buppu3/tnCart/KiCad/tnCart_rev2/tnCart_rev2.kicad_sch

## KiCad design KiCad/tnCart_rev2/tnCart_rev2.kicad_sch (2024-10-20)

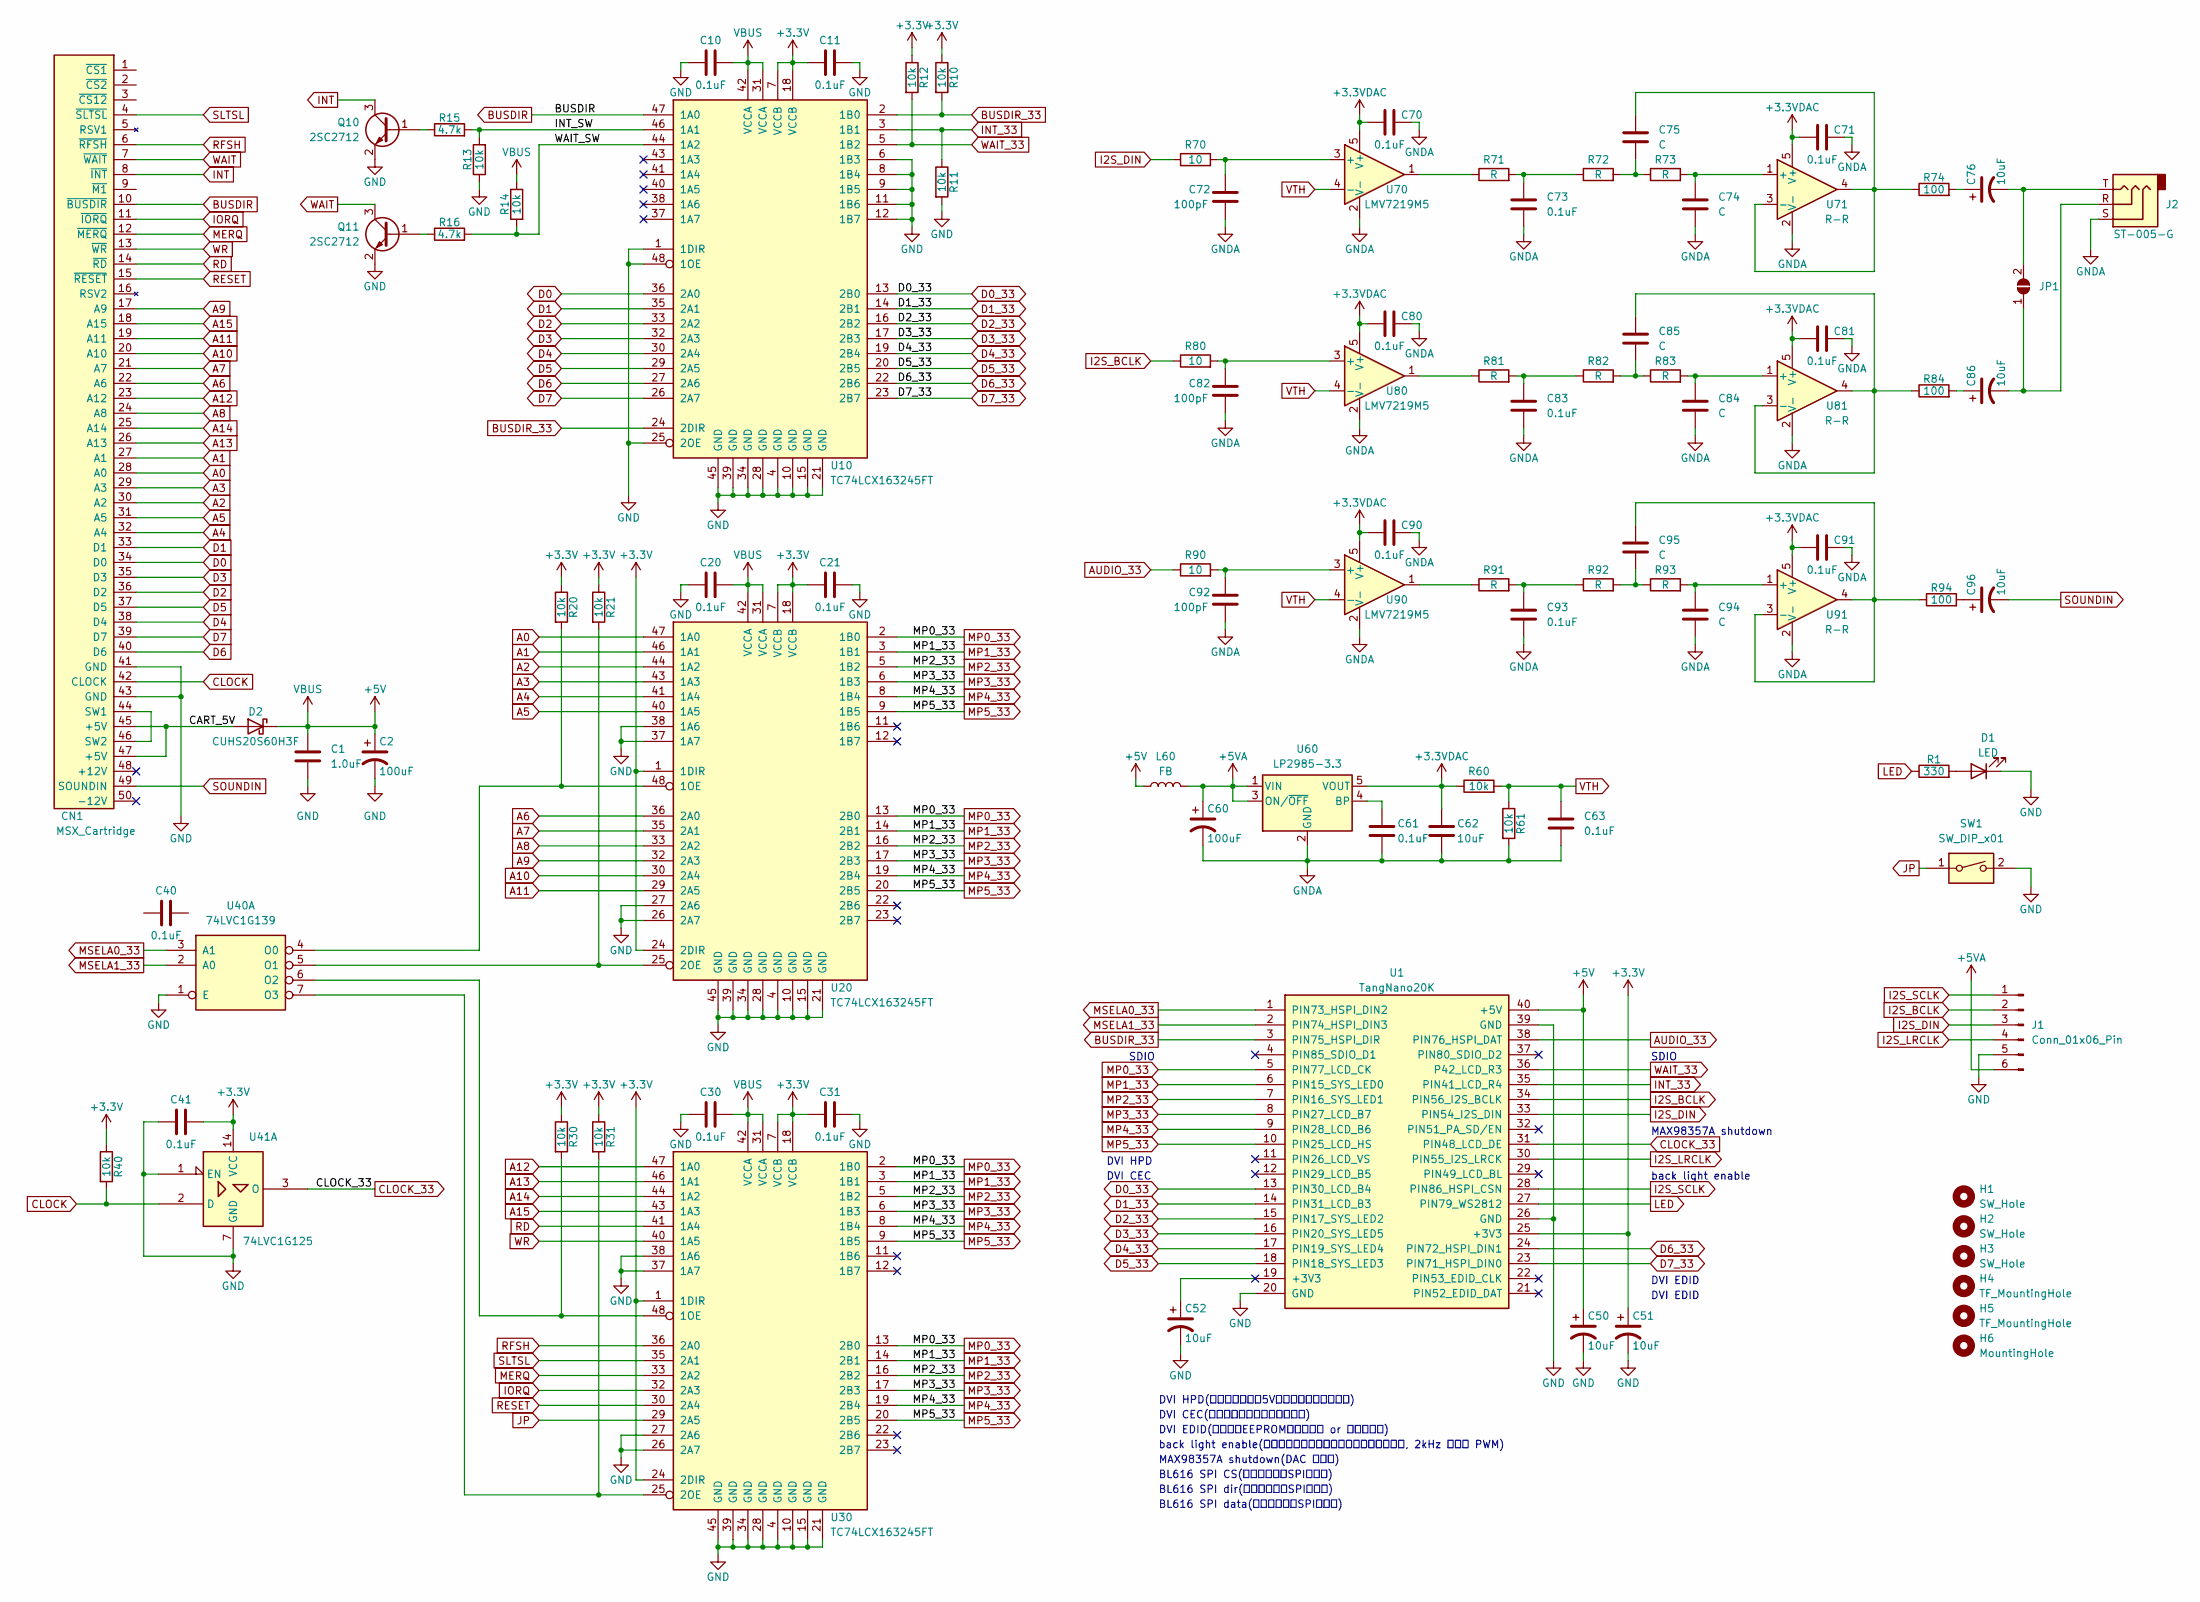
[picture p16: schematic tnCart_rev2.kicad_sch]

Parts:
C1: 1.0uF; C_0805_2012Metric_Pad1.18x1.45mm_HandSolder
C2, C60: 100uF; CP_Radial_D4.0mm_P1.50mm_Horz
C10, C11, C20, C21, C30, C31, C40, C41: 0.1uF; C_0805_2012Metric_Pad1.18x1.45mm_HandSolder
C50, C51, C52, C76, C86, C96: 10uF; CP_Radial_D4.0mm_P1.50mm_Horz
C61, C63, C70, C71, C73, C80, C81, C83, C90, C91, C93: 0.1uF
C62: 10uF
C72, C82, C92: 100pF
C74, C75, C84, C85, C94, C95: C
CN1: MSX_Cartridge; MSX_CardEdge
D1: LED; LED_D3.0mm
D2: CUHS20S60H3F; SOD-323HE_US2H
H1, H2, H3: SW_Hole; MountingHole_3.2mm_M3
H4, H5: TF_MountingHole; MountingHole_3.2mm_M3
H6: MountingHole; MountingHole_6mm
J1: Conn_01x06_Pin
J2: ST-005-G; Jack_3.5mm_Switronic_ST-005-G_horizontal
JP1: (no value)
L60: FB
Q10, Q11: 2SC2712; SC-59
R1: 330; R_0805_2012Metric_Pad1.20x1.40mm_HandSolder
R10, R11, R12, R13, R14, R20, R21, R30, R31, R40, R61: 10k; R_0805_2012Metric_Pad1.20x1.40mm_HandSolder
R15, R16: 4.7k; R_0805_2012Metric_Pad1.20x1.40mm_HandSolder
R60: 10k
R70, R80, R90: 10
R71, R72, R73, R81, R82, R83, R91, R92, R93: R
R74, R84, R94: 100; R_0805_2012Metric_Pad1.20x1.40mm_HandSolder
SW1: SW_DIP_x01
U1: TangNano20K; TangNano20k
U10, U20, U30: TC74LCX163245FT; TSSOP-48_6.1x12.5mm_P0.5mm
U40: 74LVC1G139
U41: 74LVC1G125
U60: LP2985-3.3; SOT-23-5
U70, U80, U90: LMV7219M5; SOT-23-5
U71, U81, U91: R-R; SOT-23-5

Connections:
+3.3V: C11.1, C21.1, C31.1, C41.2, C51.1, R10.1, R12.1, R20.1, R21.1, R30.1, R31.1, R40.1, U1.25 (+3V3), U10.7 (VCCB), U10.18 (VCCB), U20.1 (1DIR), U20.7 (VCCB), U20.18 (VCCB), U20.24 (2DIR), U30.1 (1DIR), U30.7 (VCCB), U30.18 (VCCB), U30.24 (2DIR), U41.14 (VCC)
+3.3VDAC: C62.1, C70.1, C71.1, C80.1, C81.1, C90.1, C91.1, R60.1, U60.5 (VOUT), U70.5 (V+), U71.5 (V+), U80.5 (V+), U81.5 (V+), U90.5 (V+), U91.5 (V+)
+5V: C1.1, C2.1, C10.2, C20.2, C30.2, C50.1, D2.1 (K), L60.1, R14.1, U1.40 (+5V), U10.31 (VCCA), U10.42 (VCCA), U20.31 (VCCA), U20.42 (VCCA), U30.31 (VCCA), U30.42 (VCCA)
+5VA: C60.1, J1.6, L60.2, U60.1 (VIN), U60.3 (ON/~OFF)
A0: CN1.28 (A0), U20.47 (1A0)
A1: CN1.27 (A1), U20.46 (1A1)
A2: CN1.30 (A2), U20.44 (1A2)
A3: CN1.29 (A3), U20.43 (1A3)
A4: CN1.32 (A4), U20.41 (1A4)
A5: CN1.31 (A5), U20.40 (1A5)
A6: CN1.22 (A6), U20.36 (2A0)
A7: CN1.21 (A7), U20.35 (2A1)
A8: CN1.24 (A8), U20.33 (2A2)
A9: CN1.17 (A9), U20.32 (2A3)
A10: CN1.20 (A10), U20.30 (2A4)
A11: CN1.19 (A11), U20.29 (2A5)
A12: CN1.23 (A12), U30.47 (1A0)
A13: CN1.26 (A13), U30.46 (1A1)
A14: CN1.25 (A14), U30.44 (1A2)
A15: CN1.18 (A15), U30.43 (1A3)
AUDIO_33: R90.1, U1.38 (PIN76_HSPI_DAT)
BUSDIR: CN1.10 (~BUSDIR), U10.47 (1A0)
BUSDIR_33: R10.2, U1.3 (PIN75_HSPI_DIR), U10.2 (1B0), U10.24 (2DIR)
CART_5V: CN1.45 (+5V), CN1.47 (+5V), D2.2 (A)
CLOCK: CN1.42 (CLOCK), R40.2, U41.2 (D)
CLOCK_33: U1.31 (PIN48_LCD_DE), U41.3 (O)
D0: CN1.34 (D0), U10.36 (2A0)
D0_33: U1.13 (PIN30_LCD_B4), U10.13 (2B0)
D1: CN1.33 (D1), U10.35 (2A1)
D1_33: U1.14 (PIN31_LCD_B3), U10.14 (2B1)
D2: CN1.36 (D2), U10.33 (2A2)
D2_33: U1.15 (PIN17_SYS_LED2), U10.16 (2B2)
D3: CN1.35 (D3), U10.32 (2A3)
D3_33: U1.16 (PIN20_SYS_LED5), U10.17 (2B3)
D4: CN1.38 (D4), U10.30 (2A4)
D4_33: U1.17 (PIN19_SYS_LED4), U10.19 (2B4)
D5: CN1.37 (D5), U10.29 (2A5)
D5_33: U1.18 (PIN18_SYS_LED3), U10.20 (2B5)
D6: CN1.40 (D6), U10.27 (2A6)
D6_33: U1.24 (PIN72_HSPI_DIN1), U10.22 (2B6)
D7: CN1.39 (D7), U10.26 (2A7)
D7_33: U1.23 (PIN71_HSPI_DIN0), U10.23 (2B7)
GND: C1.2, C2.2, C10.1, C11.2, C20.1, C21.2, C30.1, C31.2, C41.1, C50.2, C51.2, C52.2, CN1.41 (GND), CN1.43 (GND), D1.1 (K), J1.5, Q10.2 (E), Q11.2 (E), R11.2, R13.1, SW1.2, U1.20 (GND), U1.26 (GND), U1.39 (GND), U10.1 (1DIR), U10.4 (GND), U10.6 (1B3), U10.8 (1B4), U10.9 (1B5), U10.10 (GND), U10.11 (1B6), U10.12 (1B7), U10.15 (GND), U10.21 (GND), U10.25 (2OE), U10.28 (GND), U10.34 (GND), U10.39 (GND), U10.45 (GND), U10.48 (1OE), U20.4 (GND), U20.10 (GND), U20.15 (GND), U20.21 (GND), U20.26 (2A7), U20.27 (2A6), U20.28 (GND), U20.34 (GND), U20.37 (1A7), U20.38 (1A6), U20.39 (GND), U20.45 (GND), U30.4 (GND), U30.10 (GND), U30.15 (GND), U30.21 (GND), U30.26 (2A7), U30.27 (2A6), U30.28 (GND), U30.34 (GND), U30.37 (1A7), U30.38 (1A6), U30.39 (GND), U30.45 (GND), U40.1 (E), U41.1 (EN), U41.7 (GND)
GNDA: C60.2, C61.2, C62.2, C63.2, C70.2, C71.2, C72.2, C73.2, C74.2, C80.2, C81.2, C82.2, C83.2, C84.2, C90.2, C91.2, C92.2, C93.2, C94.2, J2.S, R61.2, U60.2 (GND), U70.2 (V-), U71.2 (V-), U80.2 (V-), U81.2 (V-), U90.2 (V-), U91.2 (V-)
I2S_BCLK: J1.2, R80.1, U1.34 (PIN56_I2S_BCLK)
I2S_DIN: J1.3, R70.1, U1.33 (PIN54_I2S_DIN)
I2S_LRCLK: J1.4, U1.30 (PIN55_I2S_LRCK)
I2S_SCLK: J1.1, U1.28 (PIN86_HSPI_CSN)
INT: CN1.8 (~INT), Q10.3 (C)
INT_33: R11.1, U1.35 (PIN41_LCD_R4), U10.3 (1B1)
INT_SW: R13.2, R15.2, U10.46 (1A1)
IORQ: CN1.11 (~IORQ), U30.32 (2A3)
JP: SW1.1, U30.29 (2A5)
LED: R1.1, U1.27 (PIN79_WS2812)
MERQ: CN1.12 (~MERQ), U30.33 (2A2)
MP0_33: U1.5 (PIN77_LCD_CK), U20.2 (1B0), U20.13 (2B0), U30.2 (1B0), U30.13 (2B0)
MP1_33: U1.6 (PIN15_SYS_LED0), U20.3 (1B1), U20.14 (2B1), U30.3 (1B1), U30.14 (2B1)
MP2_33: U1.7 (PIN16_SYS_LED1), U20.5 (1B2), U20.16 (2B2), U30.5 (1B2), U30.16 (2B2)
MP3_33: U1.8 (PIN27_LCD_B7), U20.6 (1B3), U20.17 (2B3), U30.6 (1B3), U30.17 (2B3)
MP4_33: U1.9 (PIN28_LCD_B6), U20.8 (1B4), U20.19 (2B4), U30.8 (1B4), U30.19 (2B4)
MP5_33: U1.10 (PIN25_LCD_HS), U20.9 (1B5), U20.20 (2B5), U30.9 (1B5), U30.20 (2B5)
MSELA0_33: U1.1 (PIN73_HSPI_DIN2), U40.3 (A1)
MSELA1_33: U1.2 (PIN74_HSPI_DIN3), U40.2 (A0)
unnamed: C52.1, U1.19 (+3V3)
unnamed: C61.1, U60.4 (BP)
unnamed: C72.1, R70.2, U70.3 (+)
unnamed: C73.1, R71.2, R72.1
unnamed: C74.1, R73.2, U71.1 (+)
unnamed: C75.1, R74.1, U71.3 (-), U71.4
unnamed: C75.2, R72.2, R73.1
unnamed: C76.1, R74.2
unnamed: C76.2, J2.T, JP1.2 (B)
unnamed: C82.1, R80.2, U80.3 (+)
unnamed: C83.1, R81.2, R82.1
unnamed: C84.1, R83.2, U81.1 (+)
unnamed: C85.1, R84.1, U81.3 (-), U81.4
unnamed: C85.2, R82.2, R83.1
unnamed: C86.1, R84.2
unnamed: C86.2, J2.R, JP1.1 (A)
unnamed: C92.1, R90.2, U90.3 (+)
unnamed: C93.1, R91.2, R92.1
unnamed: C94.1, R93.2, U91.1 (+)
unnamed: C95.1, R94.1, U91.3 (-), U91.4
unnamed: C95.2, R92.2, R93.1
unnamed: C96.1, R94.2
unnamed: CN1.44 (SW1), CN1.46 (SW2)
unnamed: D1.2 (A), R1.2
unnamed: Q10.1 (B), R15.1
unnamed: Q11.1 (B), R16.1
unnamed: R20.2, U20.48 (1OE), U40.4 (O0)
unnamed: R21.2, U20.25 (2OE), U40.5 (O1)
unnamed: R30.2, U30.48 (1OE), U40.6 (O2)
unnamed: R31.2, U30.25 (2OE), U40.7 (O3)
unnamed: R71.1, U70.1
unnamed: R81.1, U80.1
unnamed: R91.1, U90.1
RD: CN1.14 (~RD), U30.41 (1A4)
RESET: CN1.15 (~RESET), U30.30 (2A4)
RFSH: CN1.6 (~RFSH), U30.36 (2A0)
SLTSL: CN1.4 (~SLTSL), U30.35 (2A1)
SOUNDIN: C96.2, CN1.49 (SOUNDIN)
VTH: C63.1, R60.2, R61.1, U70.4 (-), U80.4 (-), U90.4 (-)
WAIT: CN1.7 (~WAIT), Q11.3 (C)
WAIT_33: R12.2, U1.36 (P42_LCD_R3), U10.5 (1B2)
WAIT_SW: R14.2, R16.2, U10.44 (1A2)
WR: CN1.13 (~WR), U30.40 (1A5)

Notes on the sheet:
SDIO
DVI HPD(モニタ接続時に5Vを分圧した電圧が入る)
BL616 SPI dir(マイコンとのSPI通信用)
DVI CEC(モニタと双方向の通信を行う)
back light enable(バックライト用のブーストコンバータ制御, 2kHz までの PWM)
DVI HPD
BL616 SPI CS(マイコンとのSPI通信用)
DVI CEC
MAX98357A shutdown
DVI EDID(モニタのEEPROMを読み出す or 双方向通信)
DVI EDID
BL616 SPI data(マイコンとのSPI通信用)
back light enable
MAX98357A shutdown(DAC の制御)
