buppu3/tnCart/rtl/src/peripheral/msx/pacrom_controller.sv

//
// pacrom_controller.sv
//
// BSD 3-Clause License
// 
// Copyright (c) 2024, Shinobu Hashimoto
// 
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
// 3. Neither the name of the copyright holder nor the names of its
//    contributors may be used to endorse or promote products derived from
//    this software without specific prior written permission.
// 
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

`default_nettype none

/***************************************************************
 * PAC ROM コントローラ
 ***************************************************************/
module PACROM_CONTROLLER #(
    parameter               RAM_ADDR_BIOS = 0,
    parameter               RAM_ADDR_PAC = 0,
    parameter               COUNT = 1,
    parameter               USE_FF = 0
) (
    input   wire            RESET_n,
    input   wire            CLK,
    BUS_IF.CARTRIDGE        Bus,
    RAM_IF.HOST             Ram,
    BUS_IF.MSX              ExtBus[0:COUNT-1],
    output wire             SramEnable
);
    localparam [15:0] BankAddr = 16'h5FFE;
    localparam [15:0] BankKey = 16'h694D;

    /***************************************************************
     * external signal
     ***************************************************************/
    logic [7:0] tmp_dout[0:COUNT-1];
    logic tmp_busdir_n[0:COUNT-1];
    logic tmp_int_n[0:COUNT-1];
    logic tmp_wait_n[0:COUNT-1];
    generate
        genvar num;
        for(num = 0; num < COUNT; num = num + 1) begin: extbus_loop
            if(USE_FF) begin
                always @(posedge CLK or negedge RESET_n) begin
                    if(!RESET_n) begin
                        ExtBus[num].ADDR        <= 0;
                        ExtBus[num].DIN         <= 0;
                        ExtBus[num].RFSH_n      <= 1;
                        ExtBus[num].RD_n        <= 1;
                        ExtBus[num].WR_n        <= 1;
                        ExtBus[num].MERQ_n      <= 1;
                        ExtBus[num].IORQ_n      <= 1;
                        ExtBus[num].CS1_n       <= 1;
                        ExtBus[num].CS2_n       <= 1;
                        ExtBus[num].CS12_n      <= 1;
                        ExtBus[num].M1_n        <= 1;
                        ExtBus[num].SLTSL_n     <= 1;
                        ExtBus[num].RESET_n     <= 0;
                        ExtBus[num].CLK         <= 0;
                        ExtBus[num].CLK_EN      <= 0;
                    end
                    else if(!Bus.RESET_n) begin
                        ExtBus[num].ADDR        <= 0;
                        ExtBus[num].DIN         <= 0;
                        ExtBus[num].RFSH_n      <= Bus.RFSH_n;
                        ExtBus[num].RD_n        <= 1;
                        ExtBus[num].WR_n        <= 1;
                        ExtBus[num].MERQ_n      <= 1;
                        ExtBus[num].IORQ_n      <= 1;
                        ExtBus[num].CS1_n       <= 1;
                        ExtBus[num].CS2_n       <= 1;
                        ExtBus[num].CS12_n      <= 1;
                        ExtBus[num].M1_n        <= 1;
                        ExtBus[num].SLTSL_n     <= 1;
                        ExtBus[num].RESET_n     <= 0;
                        ExtBus[num].CLK         <= Bus.CLK;
                        ExtBus[num].CLK_EN      <= Bus.CLK_EN;
                    end
                    else begin
                        ExtBus[num].ADDR        <= Bus.ADDR;
                        ExtBus[num].DIN         <= Bus.DIN;
                        ExtBus[num].RFSH_n      <= Bus.RFSH_n;
                        ExtBus[num].RD_n        <= Bus.RD_n;
                        ExtBus[num].WR_n        <= Bus.WR_n;
                        ExtBus[num].MERQ_n      <= Bus.MERQ_n;
                        ExtBus[num].IORQ_n      <= Bus.IORQ_n;
                        ExtBus[num].CS1_n       <= Bus.CS1_n;
                        ExtBus[num].CS2_n       <= Bus.CS2_n;
                        ExtBus[num].CS12_n      <= Bus.CS12_n;
                        ExtBus[num].M1_n        <= Bus.M1_n;
                        ExtBus[num].SLTSL_n     <= Bus.SLTSL_n;
                        ExtBus[num].RESET_n     <= Bus.RESET_n;
                        ExtBus[num].CLK         <= Bus.CLK;
                        ExtBus[num].CLK_EN      <= Bus.CLK_EN;
                    end
                end
            end
            else begin
                assign ExtBus[num].ADDR        = Bus.ADDR;
                assign ExtBus[num].DIN         = Bus.DIN;
                assign ExtBus[num].RFSH_n      = Bus.RFSH_n;
                assign ExtBus[num].RD_n        = Bus.RD_n;
                assign ExtBus[num].WR_n        = Bus.WR_n;
                assign ExtBus[num].MERQ_n      = Bus.MERQ_n;
                assign ExtBus[num].IORQ_n      = Bus.IORQ_n;
                assign ExtBus[num].CS1_n       = Bus.CS1_n;
                assign ExtBus[num].CS2_n       = Bus.CS2_n;
                assign ExtBus[num].CS12_n      = Bus.CS12_n;
                assign ExtBus[num].M1_n        = Bus.M1_n;
                assign ExtBus[num].SLTSL_n     = Bus.SLTSL_n;
                assign ExtBus[num].RESET_n     = Bus.RESET_n;
                assign ExtBus[num].CLK         = Bus.CLK;
                assign ExtBus[num].CLK_EN      = Bus.CLK_EN;
            end

            assign ExtBus[num].CLK_21M = Bus.CLK_21M;
            assign ExtBus[num].CLK_EN_21M = Bus.CLK_EN_21M;

            assign tmp_dout    [num] = ExtBus[num].DOUT     | ((num < COUNT-1) ? tmp_dout    [num + 1] : 0);
            assign tmp_busdir_n[num] = ExtBus[num].BUSDIR_n & ((num < COUNT-1) ? tmp_busdir_n[num + 1] : 1);
            assign tmp_int_n   [num] = ExtBus[num].INT_n    & ((num < COUNT-1) ? tmp_int_n   [num + 1] : 1);
            assign tmp_wait_n  [num] = ExtBus[num].WAIT_n   & ((num < COUNT-1) ? tmp_wait_n  [num + 1] : 1);
        end
    endgenerate

    if(USE_FF) begin
        always @(posedge CLK or negedge RESET_n) begin
            if(!RESET_n) begin
                Bus.INT_n          <= 1;
                Bus.WAIT_n         <= 1;
            end
            else if(!Bus.RESET_n) begin
                Bus.INT_n          <= 1;
                Bus.WAIT_n         <= 1;
            end
            else begin
                Bus.INT_n          <= tmp_int_n[0];
                Bus.WAIT_n         <= tmp_wait_n[0];
            end
        end
    end
    else begin
        assign Bus.INT_n          = tmp_int_n[0];
        assign Bus.WAIT_n         = tmp_wait_n[0];
    end

    /***************************************************************
     * アドレスデコード
     ***************************************************************/
    wire cs1_n  =  Bus.ADDR[15] || ~Bus.ADDR[14];

    /***************************************************************
     * memory read / write strobe
     ***************************************************************/
    wire wr_n = Bus.SLTSL_n || Bus.MERQ_n || Bus.WR_n;
    wire rd_n = Bus.SLTSL_n || Bus.MERQ_n || Bus.RD_n;
    wire wr_mem_n  = cs1_n || wr_n || !bank_pac;
    wire rd_mem_n  = cs1_n || rd_n;

    /***************************************************************
     * ライト検出
     ***************************************************************/
    logic prev_wr_n;
    always_ff @(posedge CLK or negedge RESET_n) begin
        if(!RESET_n)          prev_wr_n <= 1;
        else if(!Bus.RESET_n) prev_wr_n <= 1;
        else                  prev_wr_n <= wr_n;
    end
    wire det_wr = prev_wr_n && !wr_n;

    /***************************************************************
     * bank register
     ***************************************************************/
    reg [7:0] BankReg[0:1];

    always_ff @(posedge CLK or negedge RESET_n) begin
        if(!RESET_n) begin
            BankReg[0] <= 0;
            BankReg[1] <= 0;
        end
        else if(!Bus.RESET_n) begin
            BankReg[0] <= 0;
            BankReg[1] <= 0;
        end
        else if(det_wr && (Bus.ADDR[15:1] == BankAddr[15:1])) begin
            BankReg[Bus.ADDR[0]] <= Bus.DIN;
        end
    end

    /***************************************************************
     * address
     ***************************************************************/
    assign SramEnable = (BankReg[0] == BankKey[7:0]) && (BankReg[1] == BankKey[15:8]);
    wire bank_pac = SramEnable && (Bus.ADDR[15:13] == 2'b010);
    wire [23:0] addr = bank_pac ? {RAM_ADDR_PAC[23:13], Bus.ADDR[12:0]} : {RAM_ADDR_BIOS[23:14], Bus.ADDR[13:0]};

    /***************************************************************
     * memory r/w
     ***************************************************************/
    if(USE_FF) begin
        always_ff @(posedge CLK or negedge RESET_n) begin
            if(!RESET_n) begin
                Ram.ADDR <= 0;
                Ram.WE_n <= 1;
                Ram.DIN <= 0;
                Ram.DIN_SIZE <= RAM::DIN_SIZE_8;
                Ram.OE_n <= 1;
                Bus.BUSDIR_n <= 1;
                Bus.DOUT <= 0;
                Ram.RFSH_n <= 1;
            end
            else if(!Bus.RESET_n) begin
                Ram.ADDR <= 0;
                Ram.WE_n <= 1;
                Ram.DIN <= 0;
                Ram.DIN_SIZE <= RAM::DIN_SIZE_8;
                Ram.OE_n <= 1;
                Bus.BUSDIR_n <= 1;
                Bus.DOUT <= 0;
                Ram.RFSH_n <= Bus.RFSH_n;
            end
            else begin
                // address
                Ram.ADDR <= (rd_mem_n && wr_mem_n) ? 0 : addr[$bits(Ram.ADDR)-1:0];

                // memory write
                Ram.WE_n <= wr_mem_n;
                Ram.DIN <= wr_mem_n ? 0 : Bus.DIN;
                Ram.DIN_SIZE <= RAM::DIN_SIZE_8;

                // memory read
                Ram.OE_n <= rd_mem_n;
                Bus.BUSDIR_n <= rd_mem_n && tmp_busdir_n[0];
                Bus.DOUT <= tmp_busdir_n[0] ? (rd_mem_n ? 0 : Ram.DOUT[7:0]) : tmp_dout[0];

                // memory refresh
                Ram.RFSH_n <= Bus.RFSH_n;
            end
        end
    end
    else begin
        // address
        assign Ram.ADDR = (rd_mem_n && wr_mem_n) ? 0 : addr[$bits(Ram.ADDR)-1:0];

        // memory write
        assign Ram.DIN_SIZE = RAM::DIN_SIZE_8;
        assign Ram.DIN  = wr_mem_n ? 0 : Bus.DIN;
        assign Ram.WE_n = wr_mem_n;

        // memory read
        assign Ram.OE_n = rd_mem_n;
        assign Bus.BUSDIR_n = rd_mem_n && tmp_busdir_n[0];
        assign Bus.DOUT = tmp_busdir_n[0] ? (rd_mem_n ? 0 : Ram.DOUT[7:0]) : tmp_dout[0];

        // memory refresh
        assign Ram.RFSH_n = Bus.RFSH_n;
    end

endmodule


`default_nettype wire
