buppu3/tnCart/rtl/src/peripheral/sound/scc/scc.sv

//
// scc.sv
//
// BSD 3-Clause License
// 
// Copyright (c) 2024, Shinobu Hashimoto
// 
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
// 3. Neither the name of the copyright holder nor the names of its
//    contributors may be used to endorse or promote products derived from
//    this software without specific prior written permission.
// 
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

`default_nettype none

`define SCC_USE_DPB

/***************************************************************
 * SCC sound
 ***************************************************************/
module SCC (
    input wire          RESET_n,
    input wire          CLK,
    input wire          CLK_EN,

    input wire          MODE_SCC_I,

    input wire          CS_n,
    input wire [7:0]    ADDR,
    input wire          WR_n,
    input wire          RD_n,
    output wire         BUSDIR_n,
    input wire [7:0]    DIN,
    output wire [7:0]   DOUT,

    output reg [10:0]   OUT
);
    /***************************************************************
     * 読み書きタイミング
     ***************************************************************/
    wire rd_n = CS_n || RD_n;
    wire wr_n = CS_n || WR_n;
    logic prev_wr_n;
    always_ff @(posedge CLK or negedge RESET_n) begin
        if(!RESET_n)                 prev_wr_n <= 1;
        else if(!wr_n && !cs_test_n) prev_wr_n <= wr_n;
    end
    wire det_wr = prev_wr_n && !wr_n;
    wire det_rd = !rd_n;

    /***************************************************************
     * アドレスデコーダ
     ***************************************************************/
    wire cs_test_n = ADDR[7:5] != (MODE_SCC_I ? 3'b110 : 3'b111);
    wire cs_enable_n = ADDR != (MODE_SCC_I ? 8'hAF : 8'h8F);

    /***************************************************************
     * TEST レジスタ
     ***************************************************************/
    logic [7:0] test_reg;
    always_ff @(posedge CLK or negedge RESET_n) begin
        if(!RESET_n)                  test_reg <= 0;
        else if(det_wr && !cs_test_n) test_reg <= DIN;
    end

    /***************************************************************
     * ENABLE レジスタ
     ***************************************************************/
    logic [7:0] enable_reg;
    always_ff @(posedge CLK or negedge RESET_n) begin
        if(!RESET_n)                    enable_reg <= 0;
        else if(det_wr && !cs_enable_n) enable_reg <= DIN;
    end

    /***************************************************************
     * 出力更新カウンタ
     ***************************************************************/
    logic [3:0] out_cnt;
    always_ff @(posedge CLK or negedge RESET_n) begin
        if(!RESET_n)    out_cnt <= 0;
        else if(CLK_EN) out_cnt <= out_cnt + 1'd1;
    end
    wire OUT_EN = out_cnt == 0;

    /***************************************************************
     * 各チャンネルの処理
     ***************************************************************/
    logic busdir_n[0:4];
    logic [7:0] dout[0:4];
    logic [7:0] ch_out[0:4];

    generate
        genvar chnum;
        for(chnum = 0; chnum < 5; chnum = chnum + 1) begin: ch
            wire wr_freq_l = (ADDR[7:4] == (MODE_SCC_I ? 4'b1010 : 4'b1000)) && (ADDR[3:0] == chnum * 2 +  0);
            wire wr_freq_h = (ADDR[7:4] == (MODE_SCC_I ? 4'b1010 : 4'b1000)) && (ADDR[3:0] == chnum * 2 +  1);
            wire wr_vol    = (ADDR[7:4] == (MODE_SCC_I ? 4'b1010 : 4'b1000)) && (ADDR[3:0] == chnum     + 10);
            wire wr_wave   = (ADDR[7:5] == (MODE_SCC_I ? chnum[2:0] : (chnum[2] ? 3'd3 : chnum[2:0])));
            wire rd_wave   = (ADDR[7:5] == (MODE_SCC_I ? chnum[2:0] : (chnum[2] ? 3'd5 : chnum[2:0])));

            SCC_SIGNAL_GENERATOR u_gen (
                .RESET_n,
                .CLK,
                .CLK_EN,
                .TEST_CNTM  (test_reg[0]),
                .TEST_CNTH  (test_reg[1]),
                .TEST_ADDR  (test_reg[5]),
                .TEST_MEM   (chnum == 4 ? test_reg[7] : test_reg[6]),
                .ADDR       (ADDR[4:0]),
                .WR_FREQ_L_n(!det_wr || !wr_freq_l),
                .WR_FREQ_H_n(!det_wr || !wr_freq_h),
                .WR_VOL_n   (!det_wr || !wr_vol),
                .WR_WAVE_n  (!det_wr || !wr_wave),
                .RD_WAVE_n  (!det_rd || !rd_wave),
                .BUSDIR_n   (busdir_n[chnum]),
                .DIN,
                .DOUT       (dout[chnum]),
                .MUTE_n     (enable_reg[chnum]),
                .OUT_EN,
                .OUT        (ch_out[chnum])
            );
        end
    endgenerate

    /***************************************************************
     * 波形メモリのデータを CPU 側へ出力
     ***************************************************************/
    assign BUSDIR_n = busdir_n[0] && busdir_n[1] && busdir_n[2] && busdir_n[3] && busdir_n[4];
    assign DOUT = dout[0] | dout[1] | dout[2] | dout[3] | dout[4];

    /***************************************************************
     * ミキサー
     ***************************************************************/
    SCC_MIXER u_mixer (
        .RESET_n,
        .CLK,
        .CLK_EN(CLK_EN && OUT_EN),
        .IN(ch_out),
        .OUT(OUT)
    );
endmodule

/***********************************************************************
 * ミキサー
 ***********************************************************************/
module SCC_MIXER (
    input wire          RESET_n,
    input wire          CLK,
    input wire          CLK_EN,
    input wire [7:0]    IN[0:4],
    output reg [10:0]   OUT
);

    logic [10:0] in_0;
    always_ff @(posedge CLK or negedge RESET_n) begin
        if(!RESET_n)    in_0 <= 0;
        else if(CLK_EN) in_0 <= IN[0][7] ? {3'b111,IN[0]} : {3'b000,IN[0]};
    end

    logic [10:0] in_1;
    always_ff @(posedge CLK or negedge RESET_n) begin
        if(!RESET_n)    in_1 <= 0;
        else if(CLK_EN) in_1 <= IN[1][7] ? {3'b111,IN[1]} : {3'b000,IN[1]};
    end

    logic [10:0] in_2;
    always_ff @(posedge CLK or negedge RESET_n) begin
        if(!RESET_n)    in_2 <= 0;
        else if(CLK_EN) in_2 <= IN[2][7] ? {3'b111,IN[2]} : {3'b000,IN[2]};
    end

    logic [10:0] in_3;
    always_ff @(posedge CLK or negedge RESET_n) begin
        if(!RESET_n)    in_3 <= 0;
        else if(CLK_EN) in_3 <= IN[3][7] ? {3'b111,IN[3]} : {3'b000,IN[3]};
    end

    logic [10:0] in_4;
    always_ff @(posedge CLK or negedge RESET_n) begin
        if(!RESET_n)    in_4 <= 0;
        else if(CLK_EN) in_4 <= IN[4][7] ? {3'b111,IN[4]} : {3'b000,IN[4]};
    end

    always_ff @(posedge CLK or negedge RESET_n) begin
        if(!RESET_n)    OUT <= 0;
        else if(CLK_EN) OUT <= in_0 + in_1 + in_2 + in_3 + in_4;
    end

endmodule

/***********************************************************************
 * SCC 1CH シグナルジェネレータ
 ***********************************************************************/
module SCC_SIGNAL_GENERATOR (
    input wire          RESET_n,
    input wire          CLK,
    input wire          CLK_EN,

    input wire          TEST_CNTM,      // TEST.b0
    input wire          TEST_CNTH,      // TEST.b1
    input wire          TEST_ADDR,      // TEST.b5
    input wire          TEST_MEM,       // TEST.b6(ch0~3), TEST.b7(ch4)

    input wire [4:0]    ADDR,
    input wire          WR_FREQ_L_n,
    input wire          WR_FREQ_H_n,
    input wire          WR_VOL_n,
    input wire          WR_WAVE_n,
    input wire          RD_WAVE_n,
    output wire         BUSDIR_n,
    input wire  [7:0]   DIN,
    output wire  [7:0]  DOUT,

    input wire          MUTE_n,
    input wire          OUT_EN,
    output reg [7:0]    OUT
);

    logic [4:0] WAVE_ADDR;
    SCC_COUNTER u_cnt (
        .RESET_n,
        .CLK,
        .CLK_EN,
        .TEST_CNTM,
        .TEST_CNTH,
        .TEST_ADDR,
        .WR_FREQ_L_n,
        .WR_FREQ_H_n,
        .DIN,
        .WAVE_ADDR
    );

    wire [7:0] WAVE_DATA;
    SCC_WAVE_MEMORY u_mem (
        .RESET_n,
        .CLK,
        .TEST_MEM,
        .ADDR(ADDR[4:0]),
        .RD_WAVE_n,
        .WR_WAVE_n,
        .DIN,
        .BUSDIR_n,
        .DOUT,
        .WAVE_ADDR,
        .WAVE_DATA
    );

    SCC_AMP u_amp (
        .RESET_n,
        .CLK,
        .CLK_EN,
        .WR_VOL_n,
        .DIN(DIN[3:0]),
        .WAVE_DATA,
        .MUTE_n,
        .OUT_EN,
        .OUT
    );
endmodule

/***********************************************************************
 * SCC CH カウンター
 ***********************************************************************/
module SCC_COUNTER (
    input wire          RESET_n,
    input wire          CLK,
    input wire          CLK_EN,

    input wire          TEST_CNTM,      // TEST.b0
    input wire          TEST_CNTH,      // TEST.b1
    input wire          TEST_ADDR,      // TEST.b5

    input wire          WR_FREQ_L_n,
    input wire          WR_FREQ_H_n,
    input wire [7:0]    DIN,

    output reg [4:0]    WAVE_ADDR
);

    /***************************************************************
     * 分周レジスタライト
     ***************************************************************/
    logic [3:0] freq_l;
    logic [3:0] freq_m;
    logic [3:0] freq_h;
    always_ff @(posedge CLK or negedge RESET_n) begin
        if(!RESET_n) begin
            freq_l <= 0;
            freq_m <= 0;
            freq_h <= 0;
        end
        else if(!WR_FREQ_L_n) begin
            freq_l <= DIN[3:0];
            freq_m <= DIN[7:4];
        end
        else if(!WR_FREQ_H_n) begin
            freq_h <= DIN[3:0];
        end
    end

    /***************************************************************
     * カウンタの動作条件
     ***************************************************************/
    wire dec_cnt_l = CLK_EN;
    wire dec_cnt_m = (dec_cnt_l && (cnt_l == 0)) || TEST_CNTM;
    wire dec_cnt_h = (dec_cnt_m && (cnt_m == 0)) || TEST_CNTH;
    wire inc_adr   = (dec_cnt_h && (cnt_h == 0));
    wire rst_cnt   = inc_adr;
    wire rst_adr   = (TEST_ADDR && (!WR_FREQ_L_n || !WR_FREQ_H_n));

    /***************************************************************
     * 分周カウント
     ***************************************************************/
    logic [3:0] cnt_l;
    logic [3:0] cnt_m;
    logic [3:0] cnt_h;

    always_ff @(posedge CLK or negedge RESET_n) begin
        if(!RESET_n)       cnt_l <= 0;
        else if(rst_cnt)   cnt_l <= freq_l;
        else if(dec_cnt_l) cnt_l <= cnt_l - 1'd1;
    end

    always_ff @(posedge CLK or negedge RESET_n) begin
        if(!RESET_n)       cnt_m <= 0;
        else if(rst_cnt)   cnt_m <= freq_m;
        else if(dec_cnt_m) cnt_m <= cnt_m - 1'd1;
    end

    always_ff @(posedge CLK or negedge RESET_n) begin
        if(!RESET_n)       cnt_h <= 0;
        else if(rst_cnt)   cnt_h <= freq_h;
        else if(dec_cnt_h) cnt_h <= cnt_h - 1'd1;
    end

    /***************************************************************
     * アドレスカウント
     ***************************************************************/
    always_ff @(posedge CLK or negedge RESET_n) begin
        if(!RESET_n)       WAVE_ADDR <= 0;
        else if(rst_adr)   WAVE_ADDR <= 0;
        else if(inc_adr)   WAVE_ADDR <= WAVE_ADDR + 1'd1;
    end

endmodule

`ifdef SCC_USE_DPB
/***********************************************************************
 * SCC CH 波形メモリー(DPB)
 ***********************************************************************/
module SCC_WAVE_MEMORY (
    input wire          RESET_n,
    input wire          CLK,

    input wire          TEST_MEM,   // TEST.b6(ch0~3), TEST.b7(ch4)

    input wire [4:0]    ADDR,
    input wire          RD_WAVE_n,
    input wire          WR_WAVE_n,
    input wire  [7:0]   DIN,
    output wire         BUSDIR_n,
    output wire [7:0]   DOUT,

    input wire [4:0]    WAVE_ADDR,
    output wire  [7:0]  WAVE_DATA
);

    wire [7:0] dpb_read_a;  // DAC 側
    wire [7:0] dpb_read_b;  // CPU 側

    /***************************************************************
     * 波形出力
     ***************************************************************/
    assign WAVE_DATA = dpb_read_a;

    /***************************************************************
     * メモリリード
     ***************************************************************/
    assign DOUT = RD_WAVE_n ? 0 : (TEST_MEM ? dpb_read_a : dpb_read_b); // TEST_MEM == 1 の時は波形出力データを返す
    assign BUSDIR_n = RD_WAVE_n;

    /***************************************************************
     * メモリ
     ***************************************************************/
    wire [7:0] dpb_douta_w;
    wire [7:0] dpb_doutb_w;

    DPB u_dpb (
        .DOA({dpb_douta_w[7:0],dpb_read_a[7:0]}),
        .DOB({dpb_doutb_w[7:0],dpb_read_b[7:0]}),
        .CLKA(CLK),
        .OCEA(1'b1),
        .CEA(1'b1),
        .RESETA(!RESET_n),
        .WREA(1'b0),
        .CLKB(CLK),
        .OCEB(1'b1),
        .CEB(1'b1),
        .RESETB(!RESET_n),
        .WREB(!(WR_WAVE_n | TEST_MEM)),         // TEST_MEM == 1 の時はライト禁止
        .BLKSELA(3'b000),
        .BLKSELB(3'b000),
        .ADA({6'b000000,WAVE_ADDR[4:0],3'b000}),
        .DIA({8'b00000000,8'b00000000}),
        .ADB({6'b000000,ADDR[4:0],3'b000}),
        .DIB({8'b00000000,DIN[7:0]})
    );

    defparam u_dpb.READ_MODE0 = 1'b0;
    defparam u_dpb.READ_MODE1 = 1'b0;
    defparam u_dpb.WRITE_MODE0 = 2'b00;
    defparam u_dpb.WRITE_MODE1 = 2'b00;
    defparam u_dpb.BIT_WIDTH_0 = 8;
    defparam u_dpb.BIT_WIDTH_1 = 8;
    defparam u_dpb.BLK_SEL_0 = 3'b000;
    defparam u_dpb.BLK_SEL_1 = 3'b000;
    defparam u_dpb.RESET_MODE = "SYNC";
endmodule

`else

/***********************************************************************
 * SCC CH 波形メモリー(register)
 ***********************************************************************/
module SCC_WAVE_MEMORY (
    input wire          RESET_n,
    input wire          CLK,

    input wire          TEST_MEM,   // TEST.b6(ch0~3), TEST.b7(ch4)

    input wire [4:0]    ADDR,
    input wire          RD_WAVE_n,
    input wire          WR_WAVE_n,
    input wire  [7:0]   DIN,
    output reg          BUSDIR_n,
    output reg [7:0]    DOUT,

    input wire [4:0]    WAVE_ADDR,
    output reg  [7:0]   WAVE_DATA
);

    reg [7:0] buffer[0:31];

    /***************************************************************
     * メモリ R/W
     ***************************************************************/
    always_ff @(posedge CLK or negedge RESET_n) begin
        if(!RESET_n) begin
            BUSDIR_n <= 1;
            DOUT <= 0;
            WAVE_DATA <= 0;
        end
        else if(TEST_MEM) begin
            BUSDIR_n <= 1;
            DOUT <= 0;
            WAVE_DATA <= buffer[WAVE_ADDR];
        end
        else if(!WR_WAVE_n) begin
            BUSDIR_n <= 1;
            DOUT <= 0;
            WAVE_DATA <= DIN;
            buffer[ADDR] <= DIN;
        end
        else if(!RD_WAVE_n) begin
            BUSDIR_n <= 0;
            DOUT <= buffer[ADDR];
            WAVE_DATA <= buffer[ADDR];
        end
        else begin
            BUSDIR_n <= 1;
            DOUT <= 0;
            WAVE_DATA <= buffer[WAVE_ADDR];
        end
    end
endmodule

`endif

/***********************************************************************
 * SCC CH アンプ
 ***********************************************************************/
module SCC_AMP (
    input wire          RESET_n,
    input wire          CLK,
    input wire          CLK_EN,

    input wire          WR_VOL_n,
    input wire [3:0]    DIN,

    input wire [7:0]    WAVE_DATA,

    input wire          MUTE_n,
    input wire          OUT_EN,
    output reg [7:0]    OUT
);
    logic [3:0] vol;
    logic [3:0] cnt;
    logic [11:0] sum;

    /***************************************************************
     * 音量レジスタライト
     ***************************************************************/
    always_ff @(posedge CLK or negedge RESET_n) begin
        if(!RESET_n) begin
            vol <= 0;
        end
        else if(!WR_VOL_n) begin
            vol <= DIN;
        end
    end

    /***************************************************************
     * 波形データを12bitへ拡張
     ***************************************************************/
    wire [11:0] data_12bit = WAVE_DATA[7] ? {4'b1111,WAVE_DATA} : {4'b0000,WAVE_DATA};

    /***************************************************************
     * 音量の分だけ加算する
     ***************************************************************/
    always_ff @(posedge CLK or negedge RESET_n) begin
        if(!RESET_n) begin
            OUT <= 0;
            cnt <= 0;
            sum <= 0;
        end
        else if(CLK_EN) begin
            if(OUT_EN) begin
                OUT <= MUTE_n ? sum[11:4] : 0;

                if(vol != 0) begin
                    cnt <= vol - 1'd1;
                    sum <= data_12bit;
                end
                else begin
                    cnt <= 0;
                    sum <= 0;
                end
            end
            else begin
                if(cnt != 0) begin
                    cnt <= cnt - 1'd1;
                    sum <= sum + data_12bit;
                end
            end
        end
    end
endmodule

`default_nettype wire
