buppu3/tnCart/rtl/src/config.sv

//
// config.sv
//
// BSD 3-Clause License
// 
// Copyright (c) 2024, Shinobu Hashimoto
// 
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
// 3. Neither the name of the copyright holder nor the names of its
//    contributors may be used to endorse or promote products derived from
//    this software without specific prior written permission.
// 
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

`default_nettype none

/***********************************************************************************
 * メイン設定
 ***********************************************************************************/
package CONFIG;
    /***************************************************************
     * 機能に指定する定数
     ***************************************************************/
    localparam DISABLE          = 0;            // 機能の無効
    localparam ENABLE           = 1;            // 機能の有効
    localparam ENABLE_VM2413    = 1;            // 機能の有効(VM2413)
    localparam ENABLE_IKAOPLL   = 2;            // 機能の有効(IKAOPLL)
    localparam ENABLE_IKASCC    = 2;            // 機能の有効(IKASCC)
    localparam ENABLE_MEGA_SCC  = 2;            // 機能の有効(電源ON で SCC を有効)
    localparam ENABLE_MEGA_SCC_I= 3;            // 機能の有効(電源ON で SCC-I を有効)

    /***************************************************************
     * フラッシュメモリマップ
     *  00_0000 +-------------------+
     *          | bit stream(1MB)   |
     *  10_0000 +-------------------+
     *          | NEXTOR(128KB)     |
     *  12_0000 +-------------------+
     *          | FM-BIOS(16KB)     |
     *  12_4000 +-------------------+
     *          | (816KB)           |
     *  1F_0000 +-------------------+
     *          | PAC(64KB)         | (予定)
     *  20_0000 +-------------------+
     *          | MEGA ROM (2MB)    | (FLASHからMEGAROMをブートするときに使う予定)
     *  40_0000 +-------------------+
     ***************************************************************/
    localparam [23:0]   FLASH_ADDR_MEGAROM      = 24'h20_0000;
    localparam [23:0]   FLASH_SIZE_MEGAROM      = 24'h20_0000;
    localparam [23:0]   FLASH_ADDR_BIOS         = 24'h10_0000;
    localparam [23:0]   FLASH_SIZE_BIOS         = (FLASH_SIZE_BIOS_NEXTOR + FLASH_SIZE_BIOS_FM);
    localparam [23:0]   FLASH_SIZE_BIOS_NEXTOR  = 24'h02_0000;
    localparam [23:0]   FLASH_SIZE_BIOS_FM      = 24'h00_4000;
    localparam [23:0]   FLASH_ADDR_PAC          = 24'h1F_0000;
    localparam [23:0]   FLASH_SIZE_PAC          = 24'h01_0000;

    /***************************************************************
     * SD-RAM メモリマップ
     *  00_0000 +-------------------+
     *          | MEM MAPPER(4MB)   |
     *  40_0000 +-------------------+
     *          | MEGA ROM(3MB)     |
     *  70_0000 +-------------------+
     *          | NEXTOR(128KB)     |
     *  72_0000 +-------------------+
     *          | FM-BIOS(16KB)     |
     *  72_4000 +-------------------+
     *          | (360KB)           |
     *  77_E000 +-------------------+
     *          | PAC(8KB)          |
     *  78_0000 +-------------------+
     *          | VRAM(512KB)       |
     *  80_0000 +-------------------+
     ***************************************************************/
    localparam [23:0]   RAM_ADDR_RAM            = 24'h00_0000;
    localparam [23:0]   RAM_SIZE_RAM            = 24'h40_0000;
    localparam [23:0]   RAM_ADDR_MEGAROM        = 24'h40_0000;
    localparam [23:0]   RAM_SIZE_MEGAROM        = 24'h30_0000;
    localparam [23:0]   RAM_ADDR_BIOS           = 24'h70_0000;
    localparam [23:0]   RAM_ADDR_BIOS_NEXTOR    = RAM_ADDR_BIOS;
    localparam [23:0]   RAM_ADDR_BIOS_FM        = (RAM_ADDR_BIOS_NEXTOR + FLASH_SIZE_BIOS_NEXTOR);
    localparam [23:0]   RAM_ADDR_PAC            = 24'h77_E000;
    localparam [23:0]   RAM_ADDR_VRAM           = 24'h78_0000;

    /***************************************************************
     * アッテネータ
     ***************************************************************/
    // 3.5mm ジャック
    localparam          ATT_EXT_PSG_MUL         = 1;
    localparam          ATT_EXT_PSG_DIV         = 1;
    localparam          ATT_EXT_FM_MUL          = 1;
    localparam          ATT_EXT_FM_DIV          = 1;
    localparam          ATT_EXT_MEGAROM_MUL     = 1;
    localparam          ATT_EXT_MEGAROM_DIV     = 1;

    // MSX 本体側
    localparam          ATT_INT_FM_MUL          = 9;
    localparam          ATT_INT_FM_DIV          = 4;
    localparam          ATT_INT_MEGAROM_MUL     = 9;
    localparam          ATT_INT_MEGAROM_DIV     = 4;

    /***************************************************************
     * 機能
     ***************************************************************/
    localparam          ENABLE_MEGAROM          = ENABLE;           // メガロムカートリッジを有効にするか(DISABLE/ENABLE/ENABLE_MEGA_SCC/ENABLE_MEGA_SCC_I)
    localparam          ENABLE_FM               = ENABLE_IKAOPLL;   // FM 音源カートリッジを有効にするか(DISABLE/ENABLE_VM2413/ENABLE_IKAOPLL)
    localparam          ENABLE_NEXTOR           = ENABLE;           // NEXTOR カートリッジを有効にするか(DISABLE/ENABLE)
    localparam          ENABLE_RAM              = ENABLE;           // 拡張 RAM カートリッジを有効にするか(DISABLE/ENABLE)
    localparam          ENABLE_PSG              = ENABLE;           // PSG を有効にするか(DISABLE/ENABLE)
    localparam          ENABLE_SCC              = ENABLE;           // SCC を有効にするか(DISABLE/ENABLE/ENABLE_IKASCC)
    localparam          ENABLE_V9990            = ENABLE;           // V9990 を有効にするか(DISABLE/ENABLE)
    localparam          ENABLE_V9990_CMD        = ENABLE;           // V9990 の VDP コマンドを有効(V9990のVDPコマンドを有効にすると回路の規模が大きくなるので、他の大きな機能と同時使用はできない)
    localparam          ENABLE_PAC_WRITE        = ENABLE;           // PAC データを FLASH に保存するか(DISABLE/ENABLE)
    localparam          ENABLE_SCANLINE         = DISABLE;          // 200ラインモード時に走査線の隙間を空ける

    localparam          ENABLE_DAC_I2S          = DISABLE;          // I2S DAC を使用するか(DISABLE/ENABLE)
    localparam          ENABLE_DAC_STEREO       = DISABLE;          // ステレオ出力を有効にするか(DISABLE/ENABLE)

    /***************************************************************
     * other(ここを変更すると動作しなくなる可能性があります)
     ***************************************************************/
    localparam          RAM_IF_EXPANSION_USES_FF= 0;                // RAM I/F 拡張動作に FF を使用(0=使用しない/1=使用する)
    localparam          SLOT_EXPANSION_USES_FF  = 1;                // SLOT 拡張に FF を使用(0=使用しない/1=使用する)
    localparam          SOUND_BIT_WIDTH         = 10;               // サウンド生成の量子化幅(bits)
endpackage

`default_nettype wire
